MPihlap/Frequency-Lock/firmware/Inc/note_freq.h

// Different pitches in Hz

#define G5 787
#define A5 884
#define B5 992
#define C6 1051
#define D6 1180
#define E6 1324
#define F6_SHARP 1486
#define G6 1575

// How many notes need to be played
#define LOCK_STAGES MY_HEART_WILL_GO_ON_LEN
#define THE_LICK \
  { G5, A5, B5, C6, B5, G5, A5 }
#define THE_LICK_LEN 7
#define MY_HEART_WILL_GO_ON \
  { G5, A5, B5, A5, G5, A5, D6, C6, B5, G5 }
#define MY_HEART_WILL_GO_ON_LEN 10
